VentCU/bbwtb/electronics/schematics/variantA.png

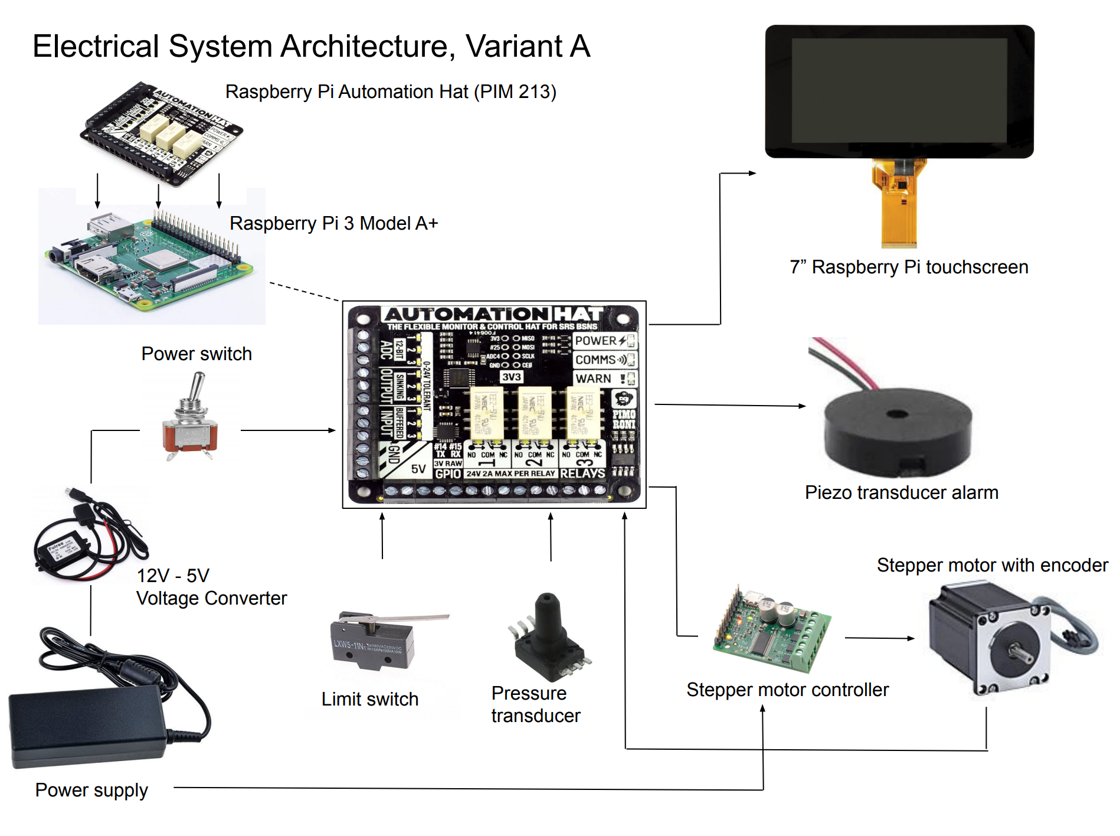
electronics/schematics/variantA.png
