VentCU/bbwtb/electronics/schematics/variantB.png

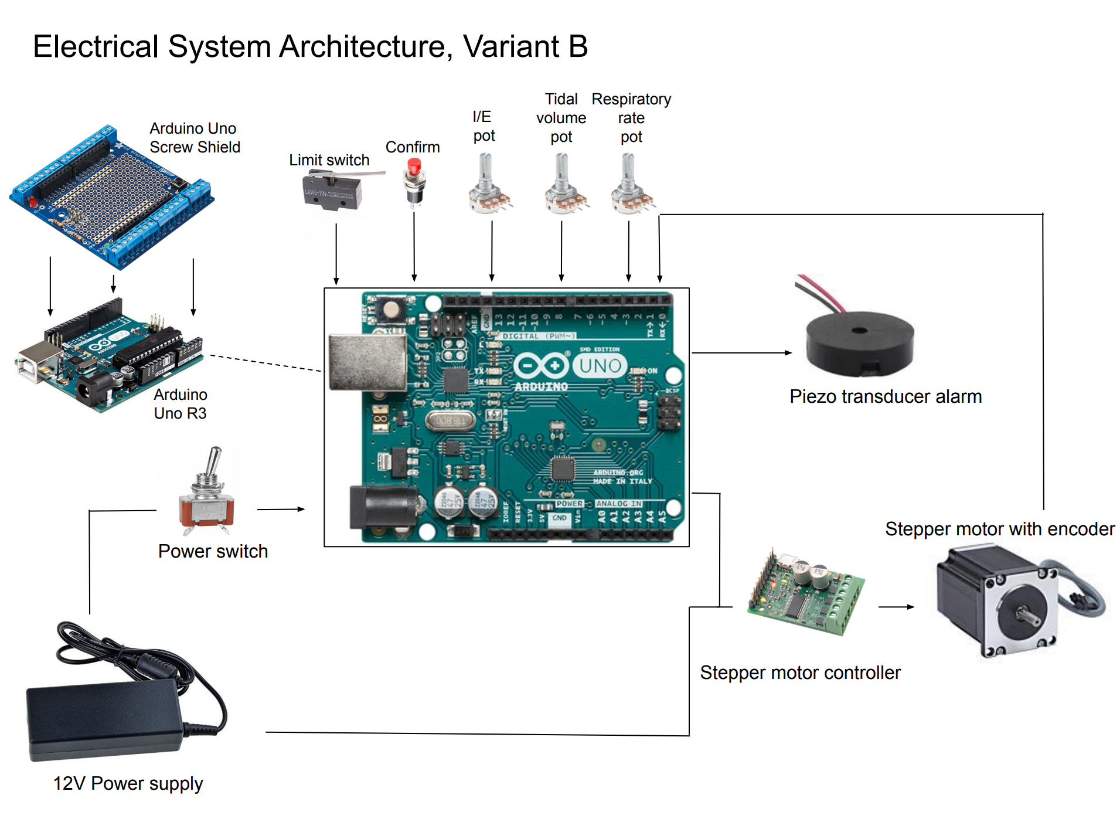
electronics/schematics/variantB.png
