VentCU/bbwtb/media/controls_labeled_exploded.jpg

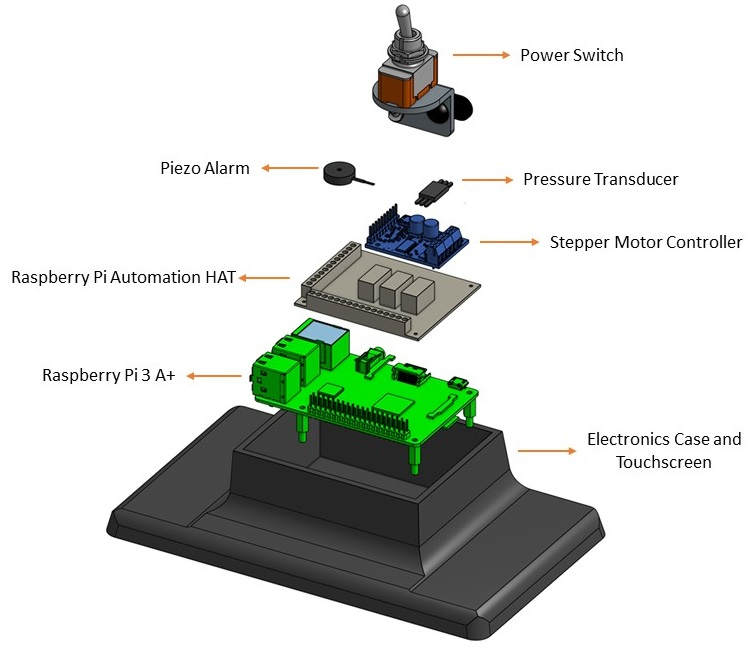
media/controls_labeled_exploded.jpg
