VentCU/bbwtb/media/frontleft_render.png

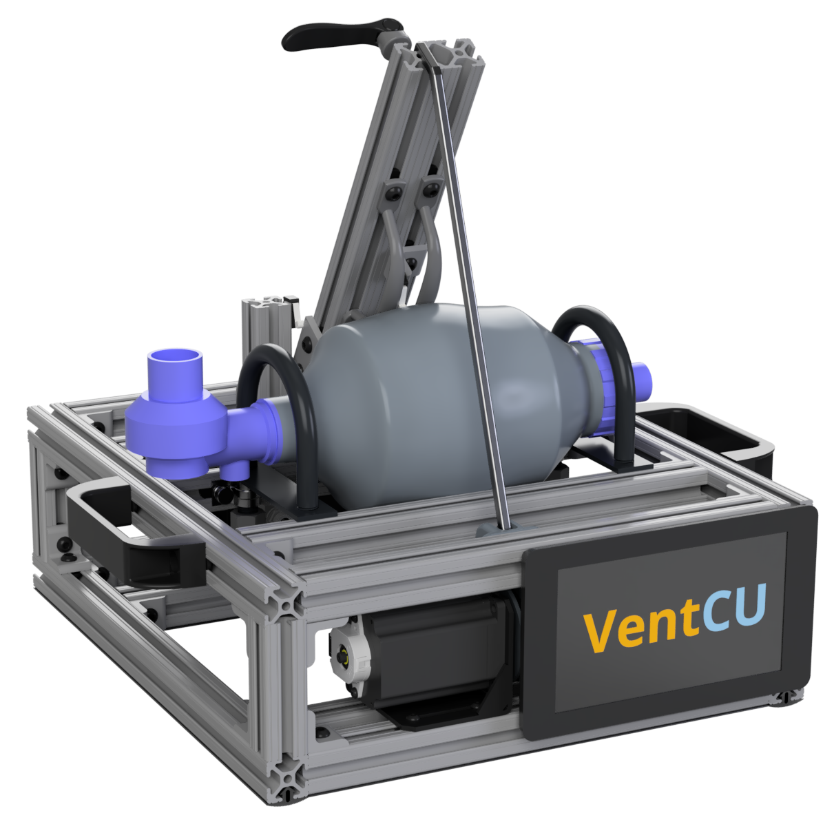
media/frontleft_render.png
