VentCU/bbwtb/media/labeled_exploded.jpg

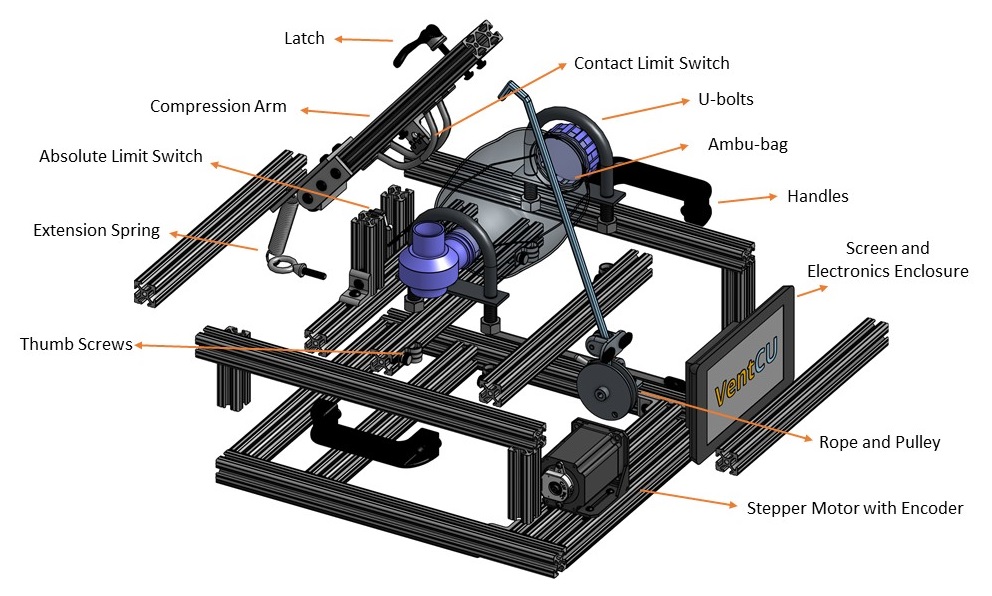
media/labeled_exploded.jpg
