VentCU/bbwtb/media/profiles/frontback.png

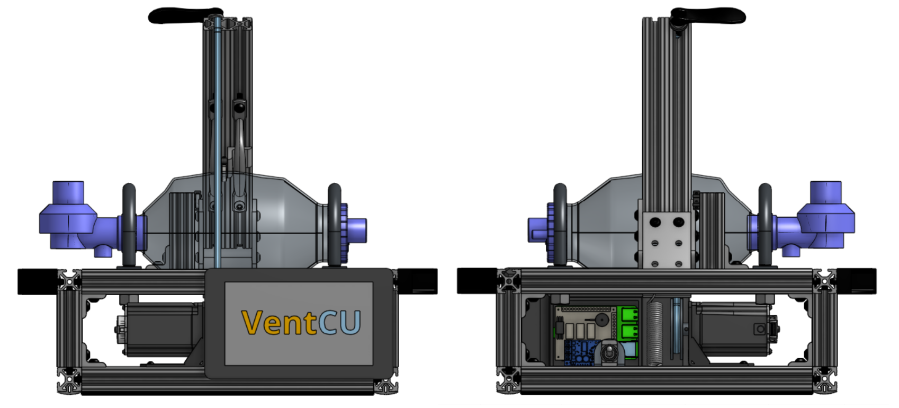
media/profiles/frontback.png
