VentCU/bbwtb/media/profiles/leftright.png

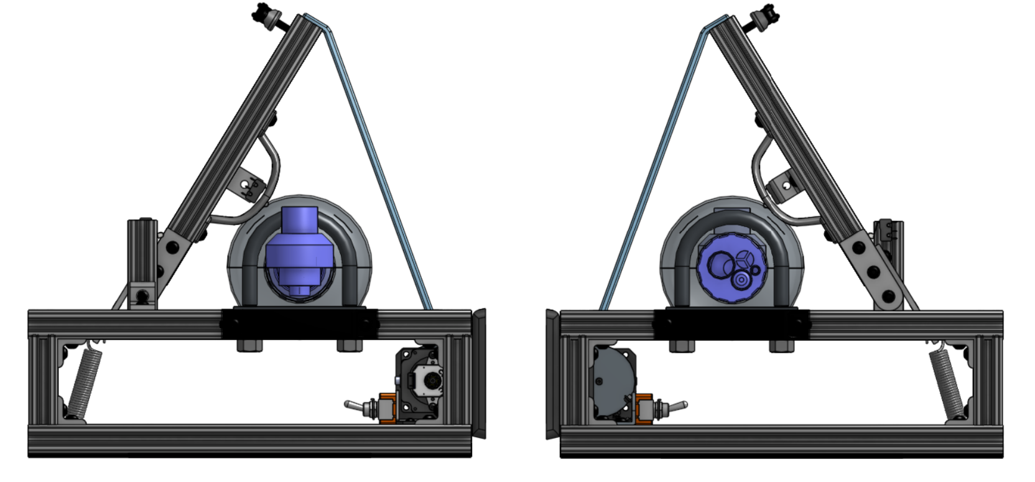
media/profiles/leftright.png
