VentCU/bbwtb/media/profiles/topbottom.png

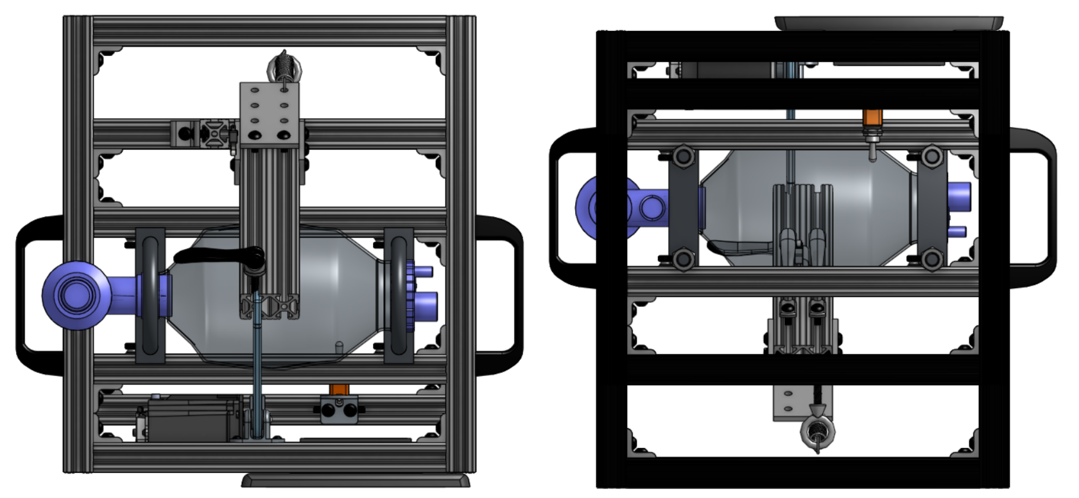
media/profiles/topbottom.png
