VentCU/bbwtb/media/render_with_ui.png

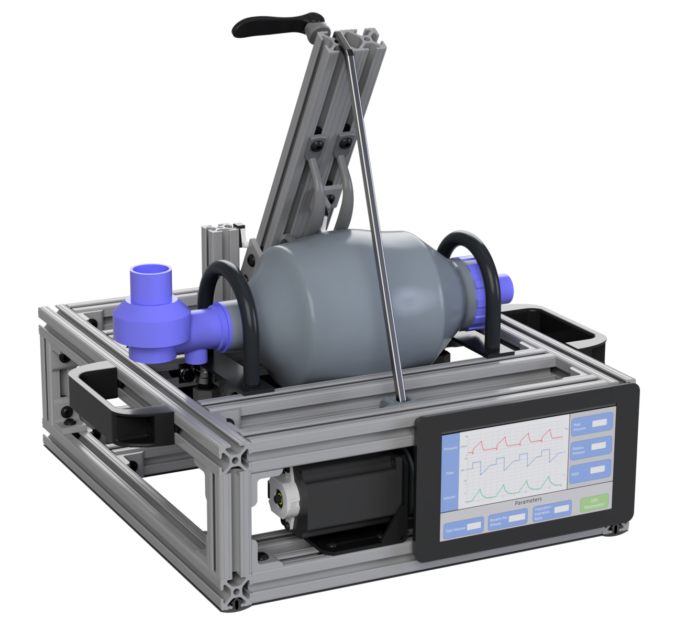
media/render_with_ui.png
