VentCU/bbwtb/media/v1/delphinefreebody.png

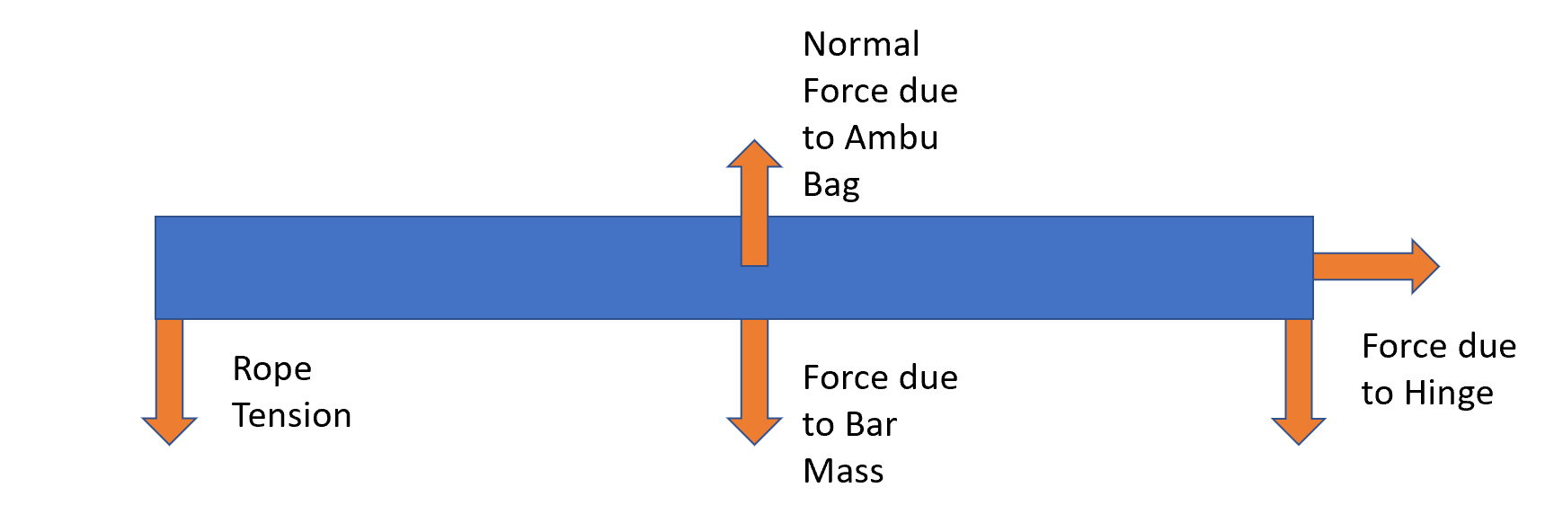
media/v1/delphinefreebody.png
