VentCU/bbwtb/media/v1/ventcu home view.PNG

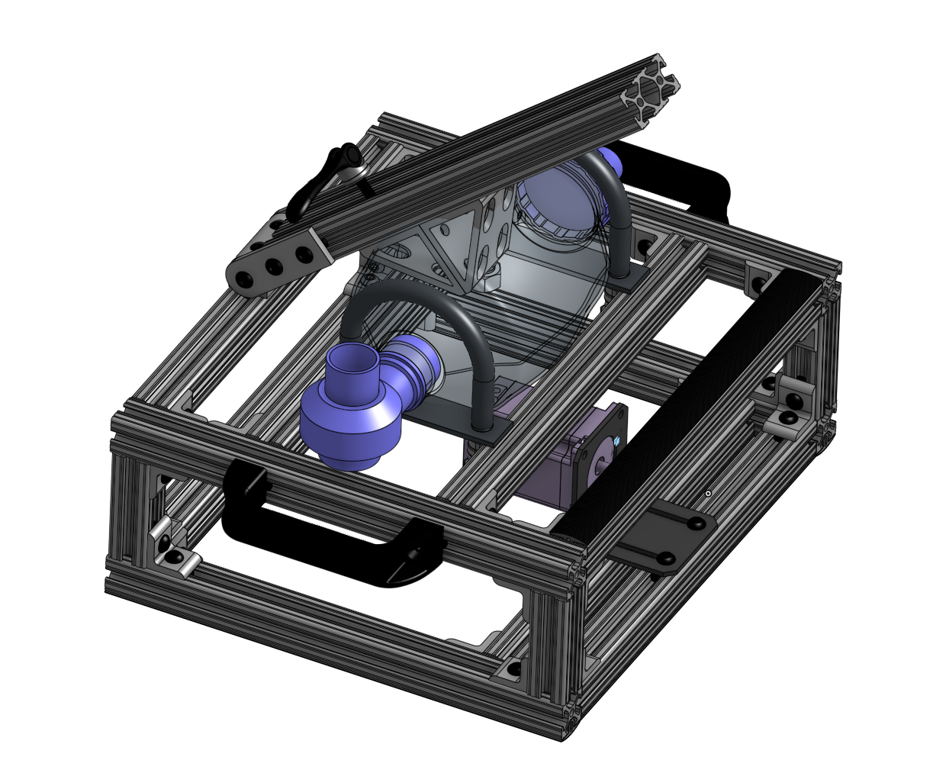
media/v1/ventcu home view.PNG
