VentCU/bbwtb/software/documentation/mock_ui.png

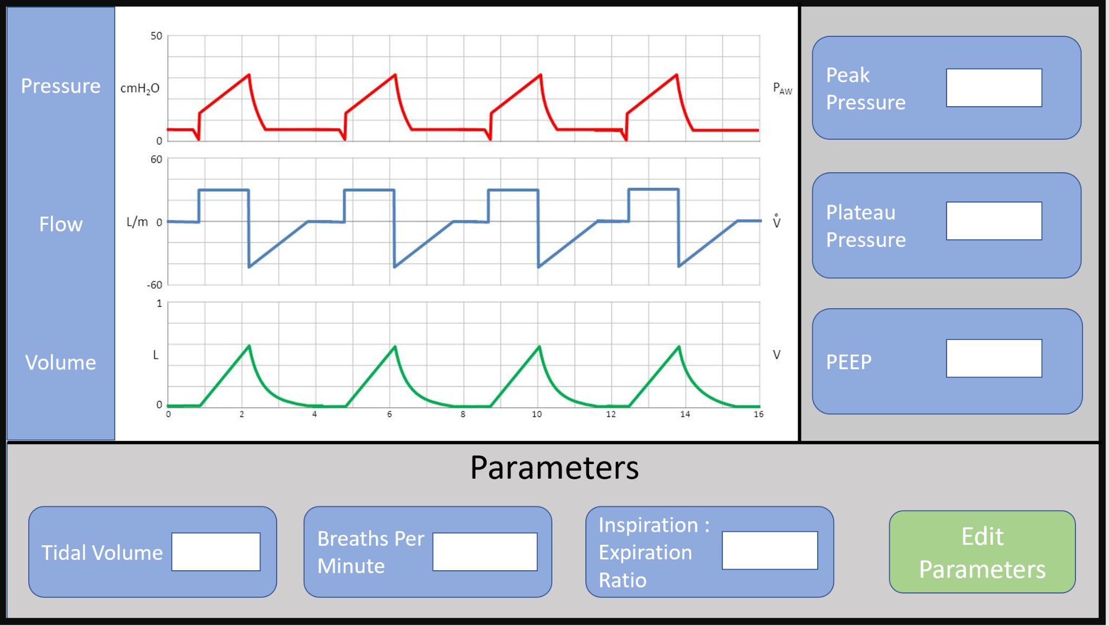
software/documentation/mock_ui.png
