VentCU/bbwtb/software/documentation/ui_alarm.PNG

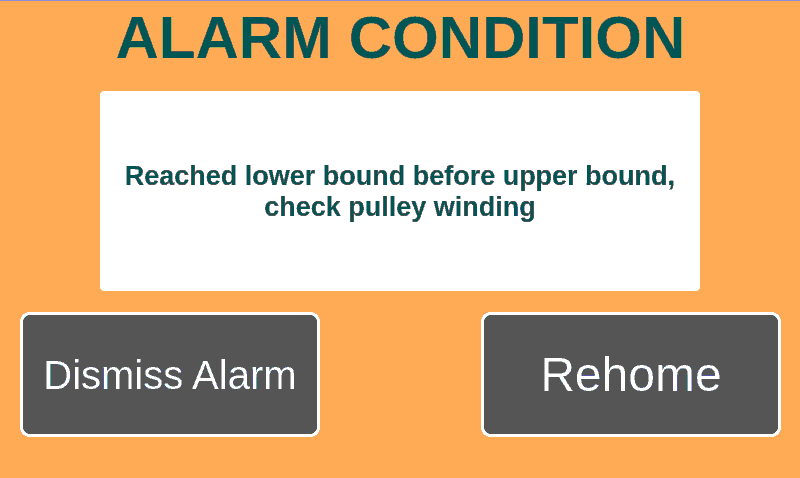
software/documentation/ui_alarm.PNG
