VentCU/bbwtb/software/documentation/ui_confirm_param.PNG

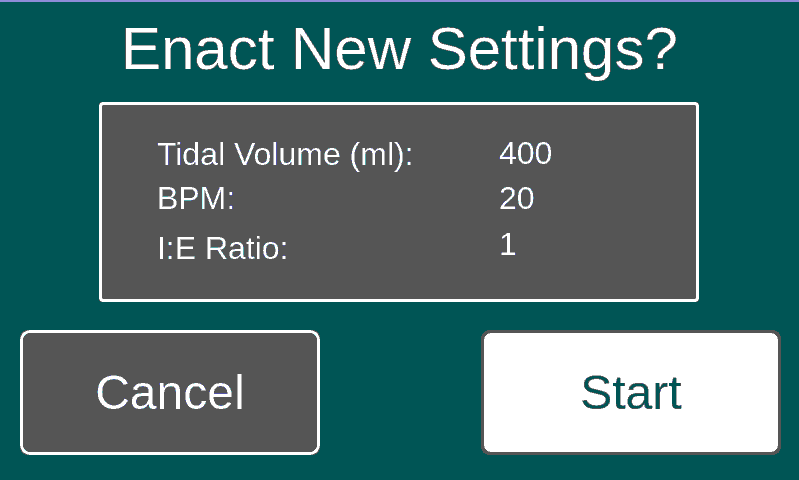
software/documentation/ui_confirm_param.PNG
