VentCU/bbwtb/software/documentation/ui_edit_param.PNG

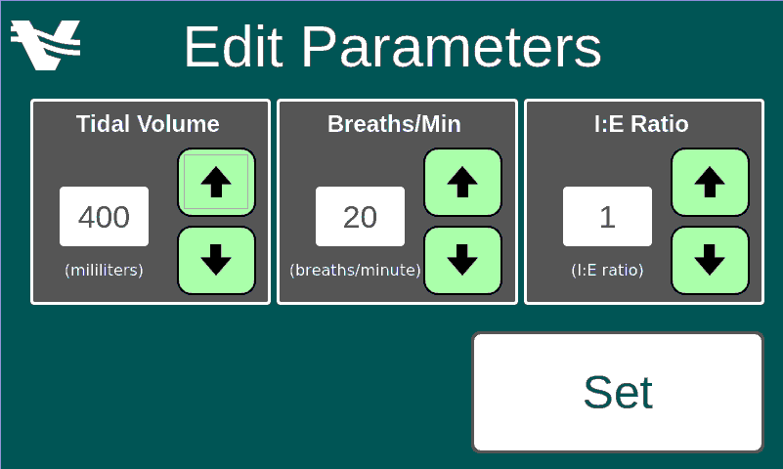
software/documentation/ui_edit_param.PNG
