VentCU/bbwtb/software/documentation/ui_home.PNG

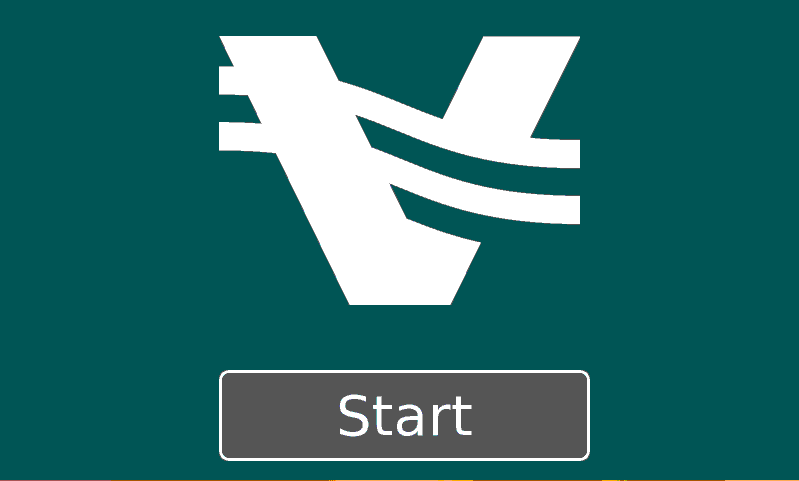
software/documentation/ui_home.PNG
