VentCU/bbwtb/software/documentation/ui_homing.PNG

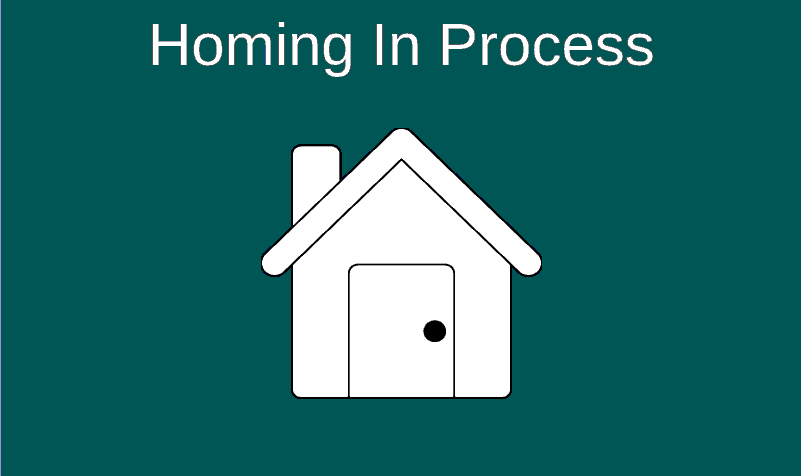
software/documentation/ui_homing.PNG
