VentCU/bbwtb/software/documentation/ui_main_page.PNG

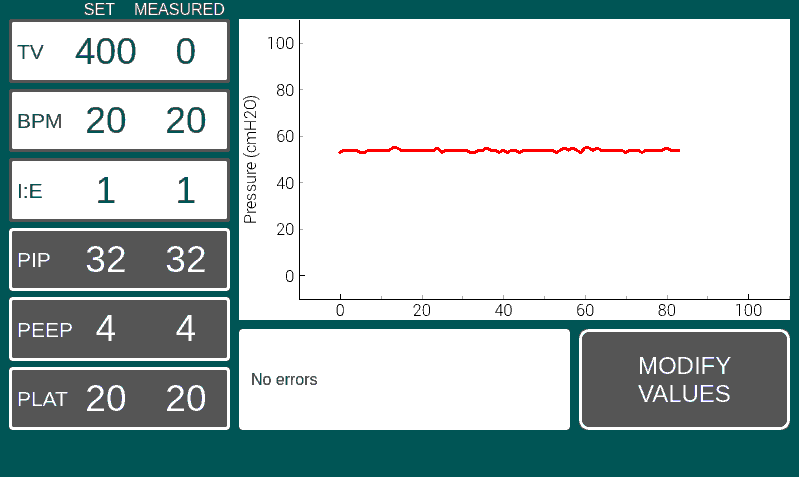
software/documentation/ui_main_page.PNG
