VentCU/bbwtb/media/v1/Case Assembly exploded view labeled.png

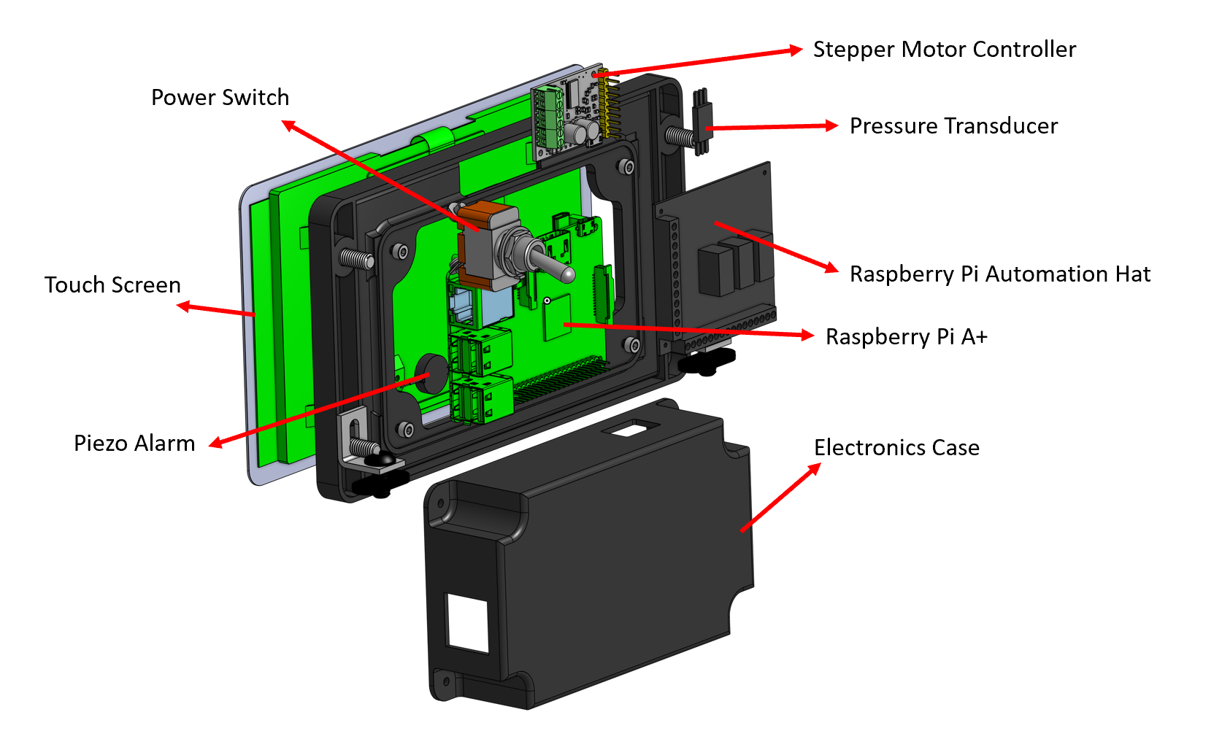
media/v1/Case Assembly exploded view labeled.png
