VentCU/bbwtb/media/v1/Case Assembly exploded view.png

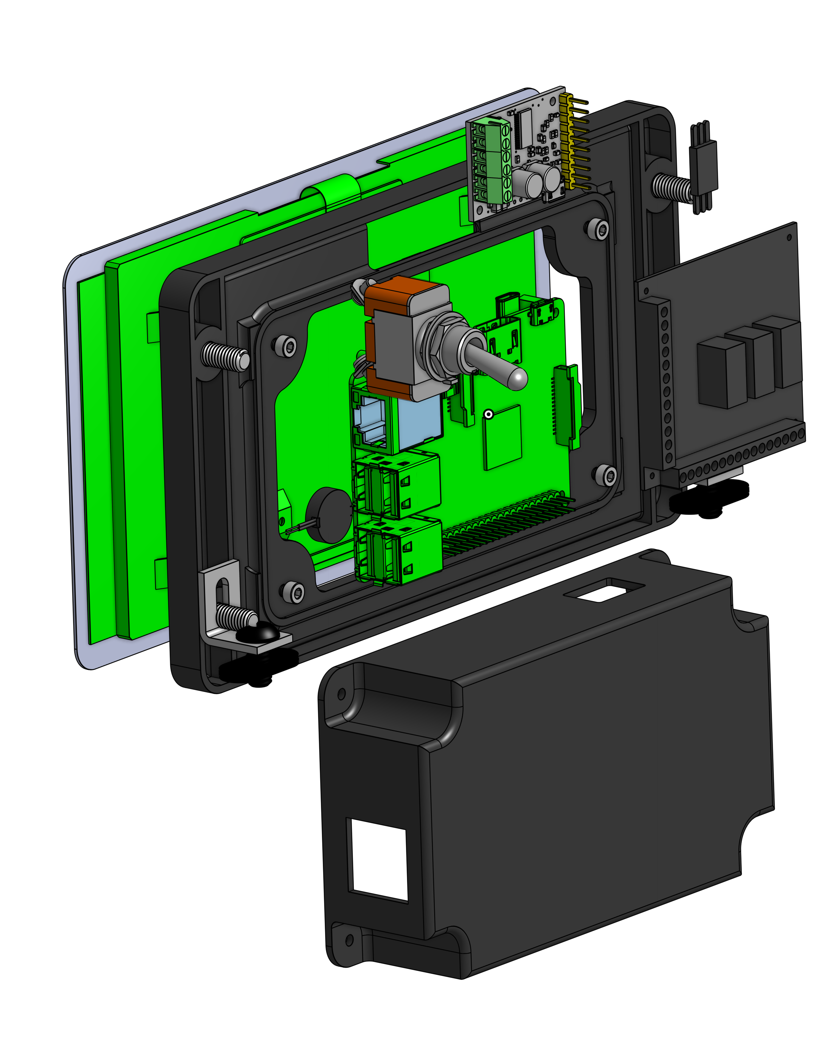
media/v1/Case Assembly exploded view.png
