VentCU/bbwtb/media/v1/Main Assembly back view.png

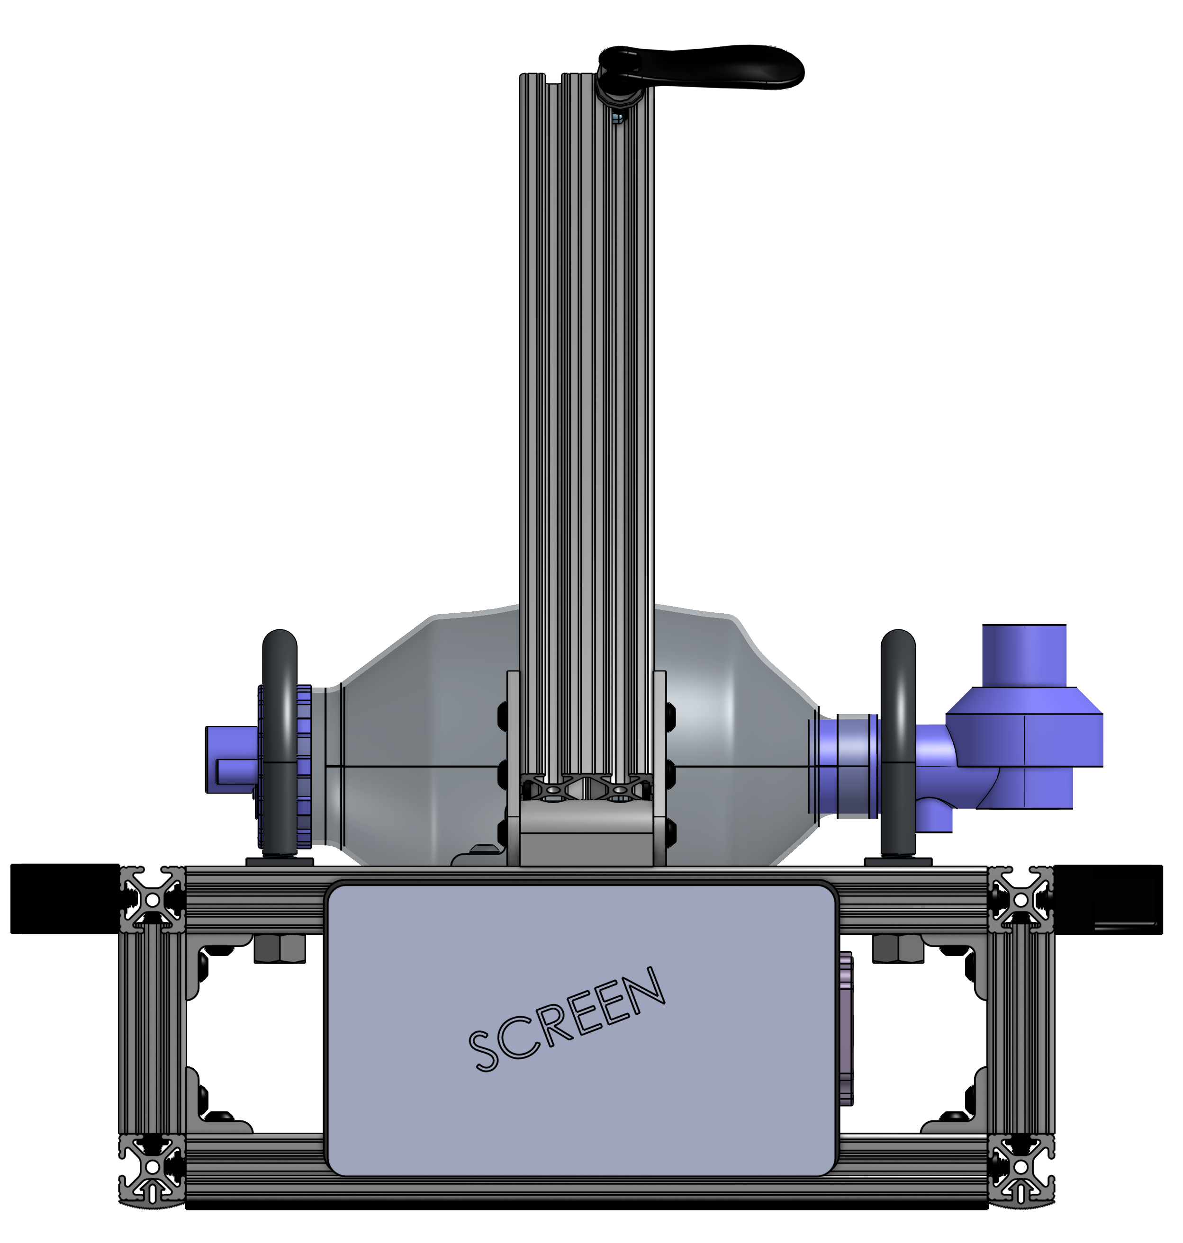
media/v1/Main Assembly back view.png
