VentCU/bbwtb/media/v1/Main Assembly bad render.png

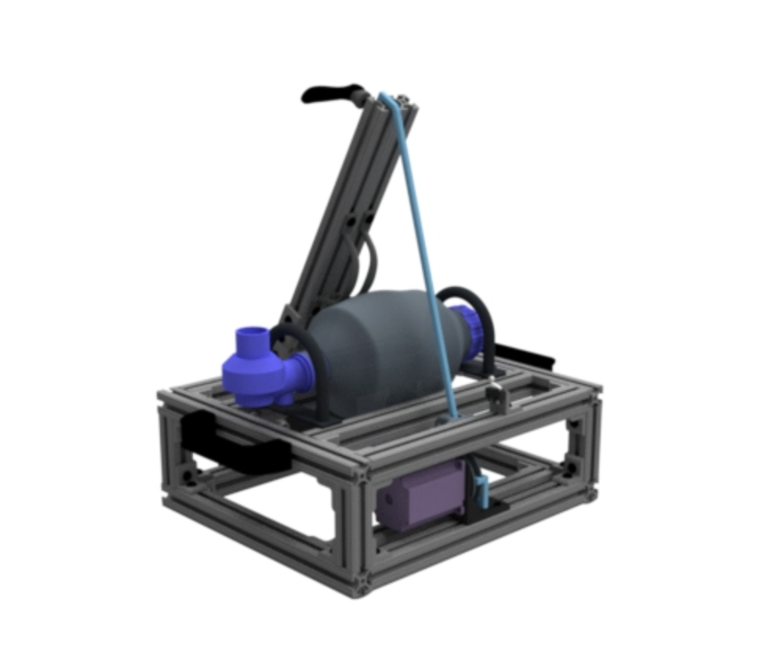
media/v1/Main Assembly bad render.png
