VentCU/bbwtb/media/v1/Main Assembly bottom view.png

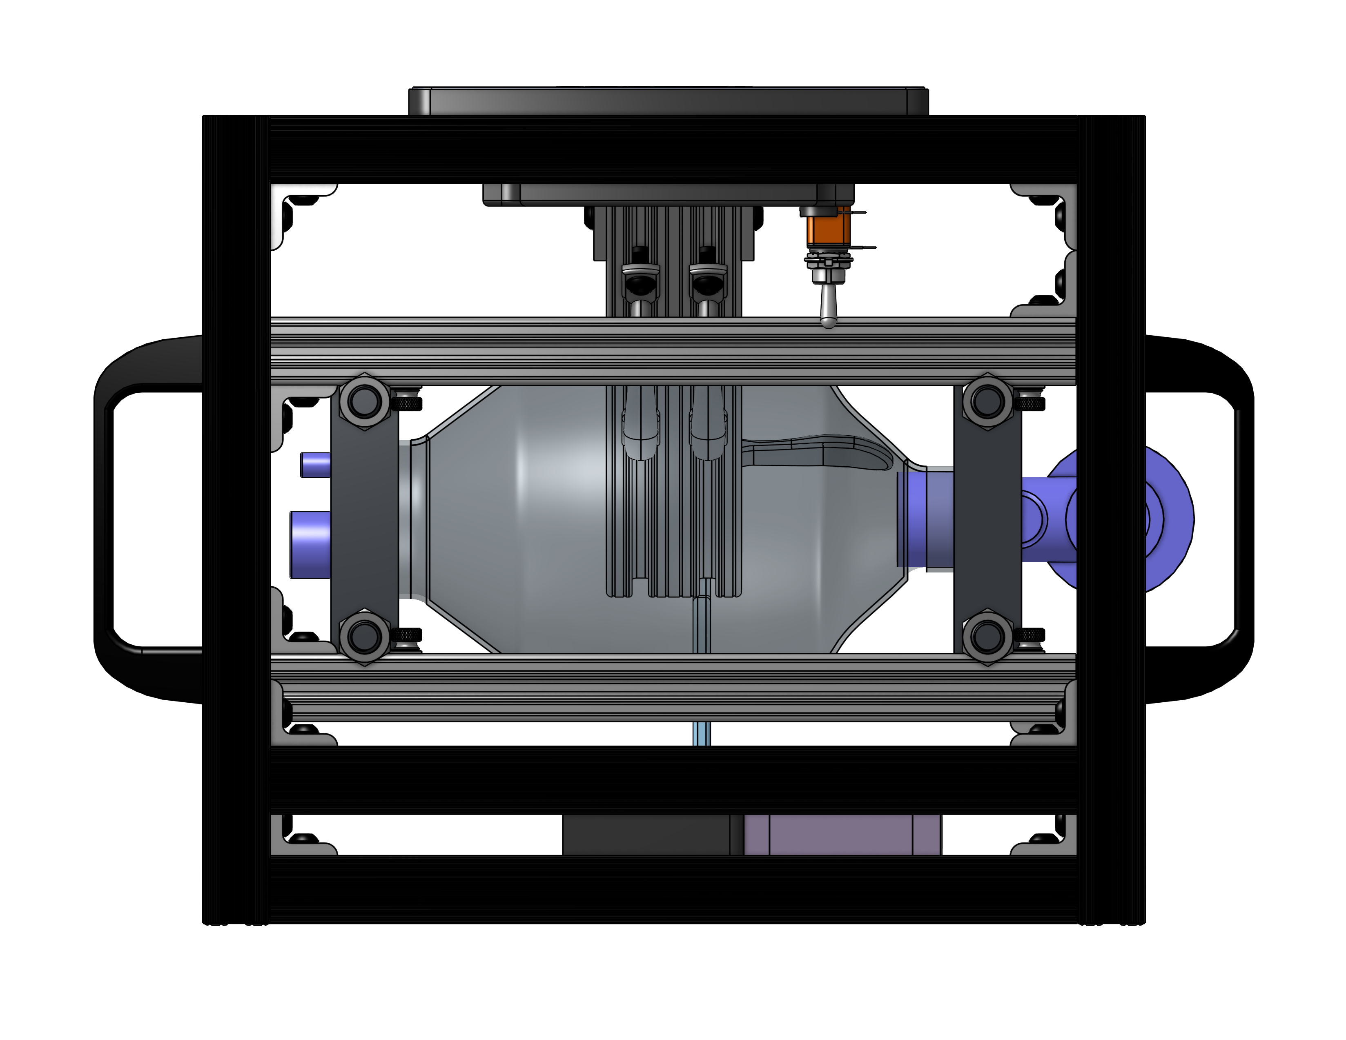
media/v1/Main Assembly bottom view.png
