VentCU/bbwtb/media/v1/Main Assembly exploded view labeled.png

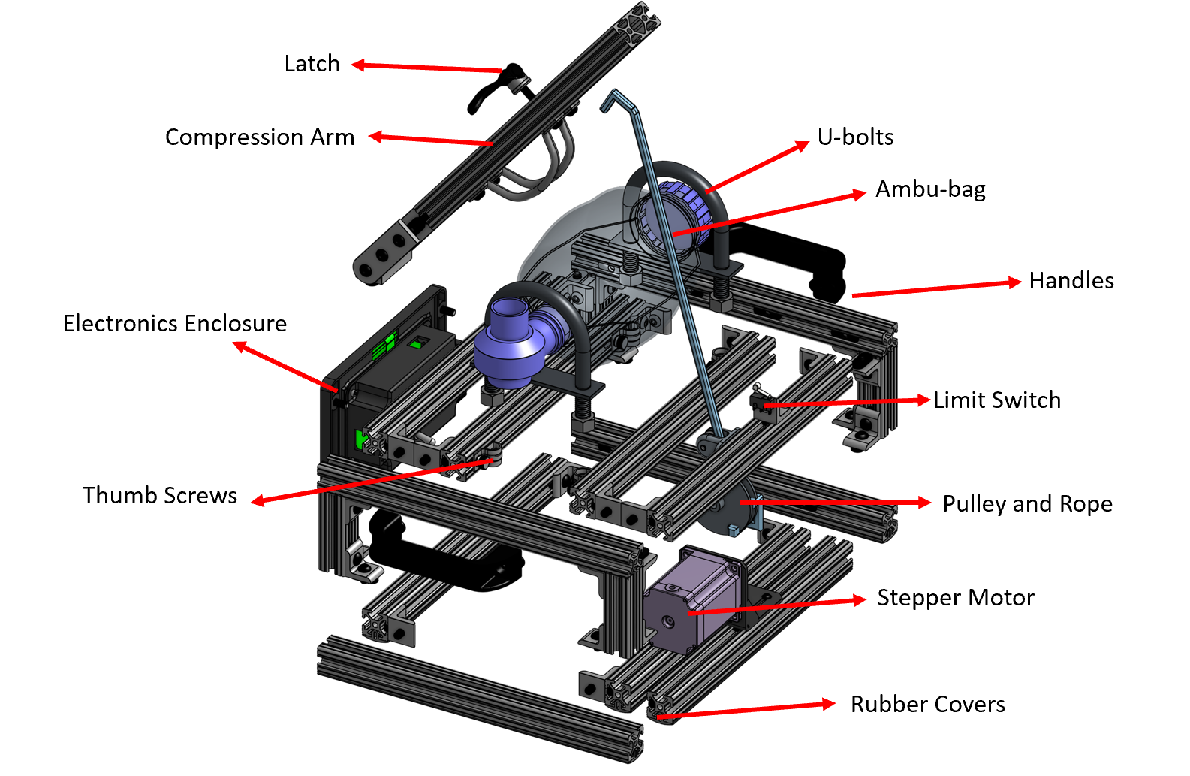
media/v1/Main Assembly exploded view labeled.png
