VentCU/bbwtb/media/v1/Main Assembly front and back view.png

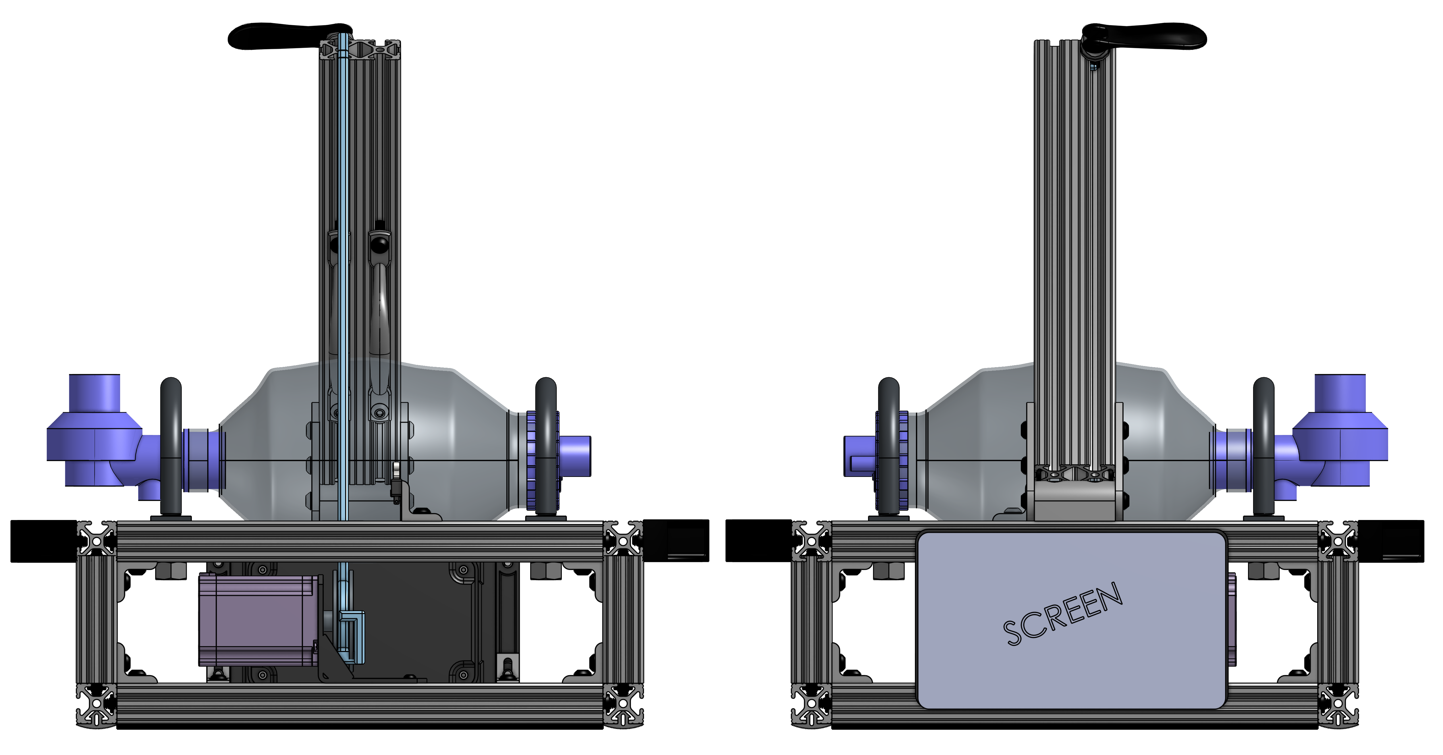
media/v1/Main Assembly front and back view.png
