VentCU/bbwtb/media/v1/Main Assembly home view alt.png

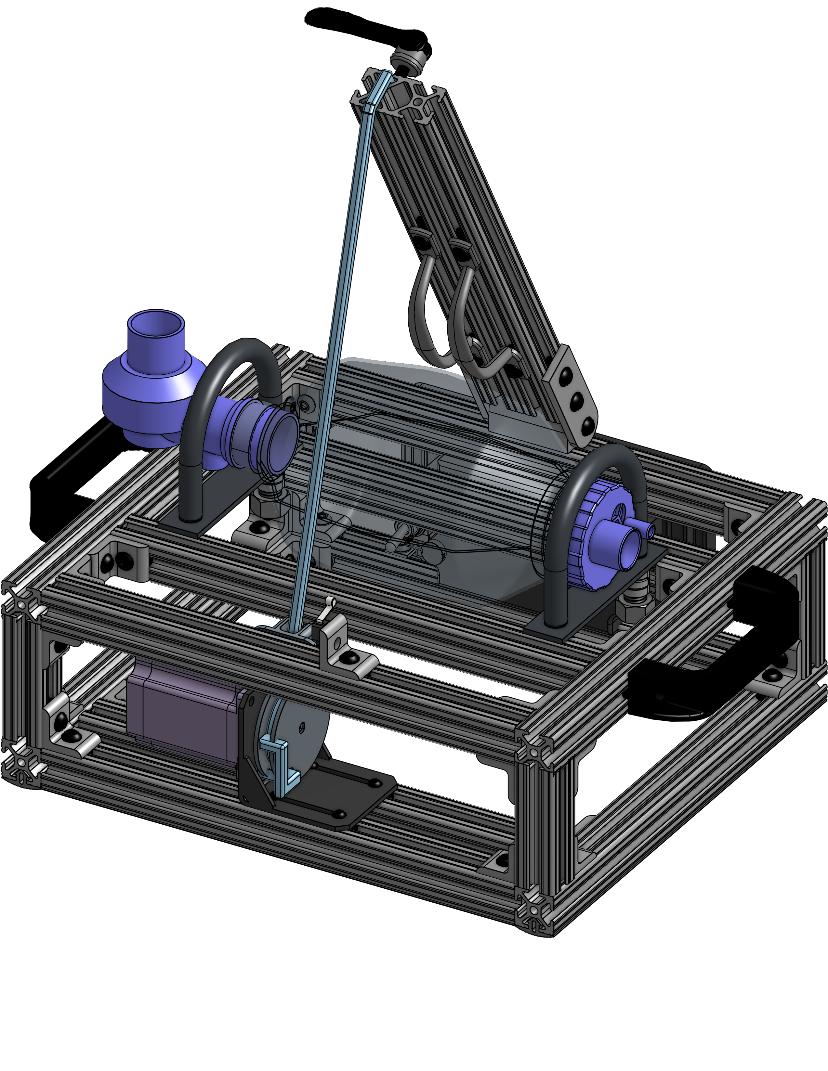
media/v1/Main Assembly home view alt.png
