VentCU/bbwtb/media/v1/Main Assembly left side view.png

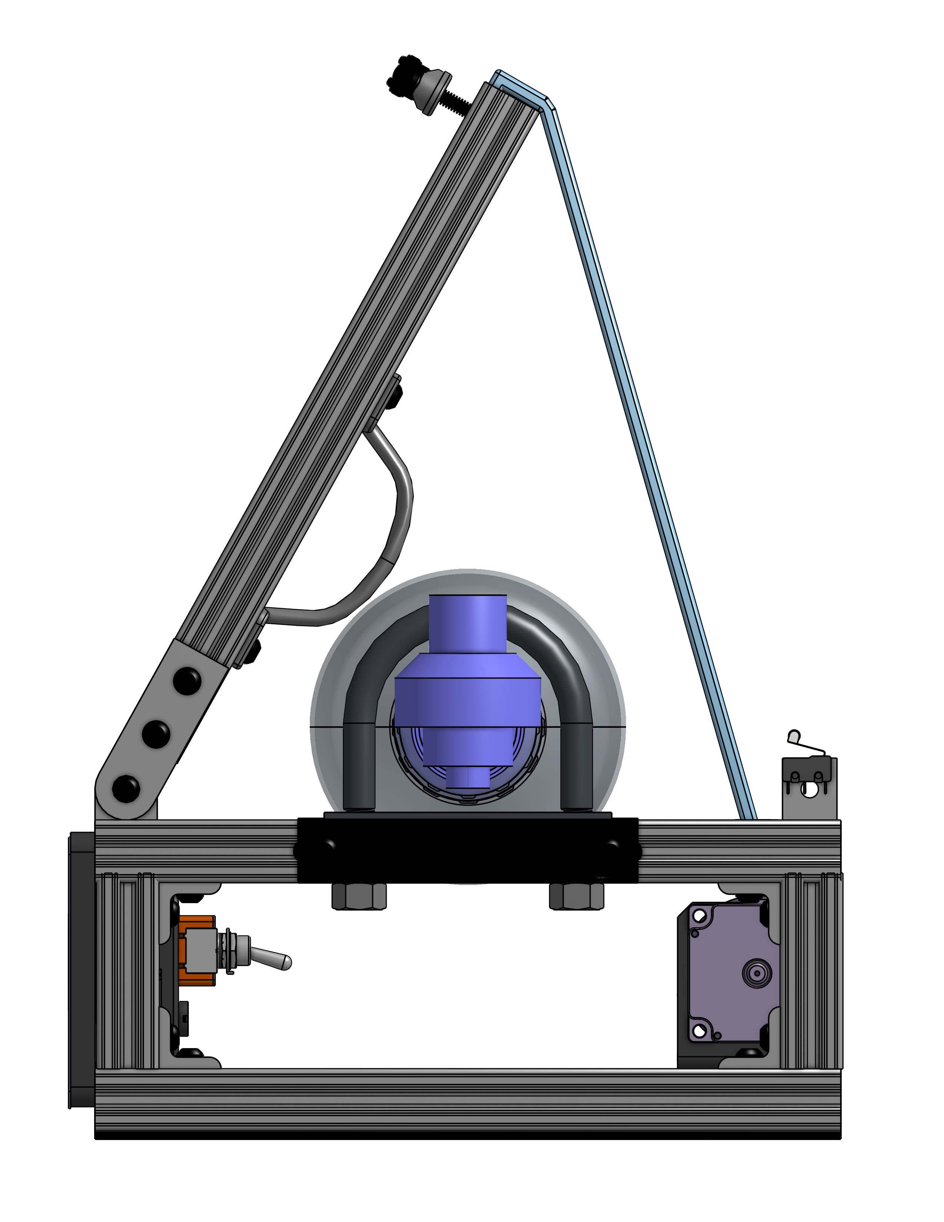
media/v1/Main Assembly left side view.png
