VentCU/bbwtb/media/v1/Main Assembly right side view.png

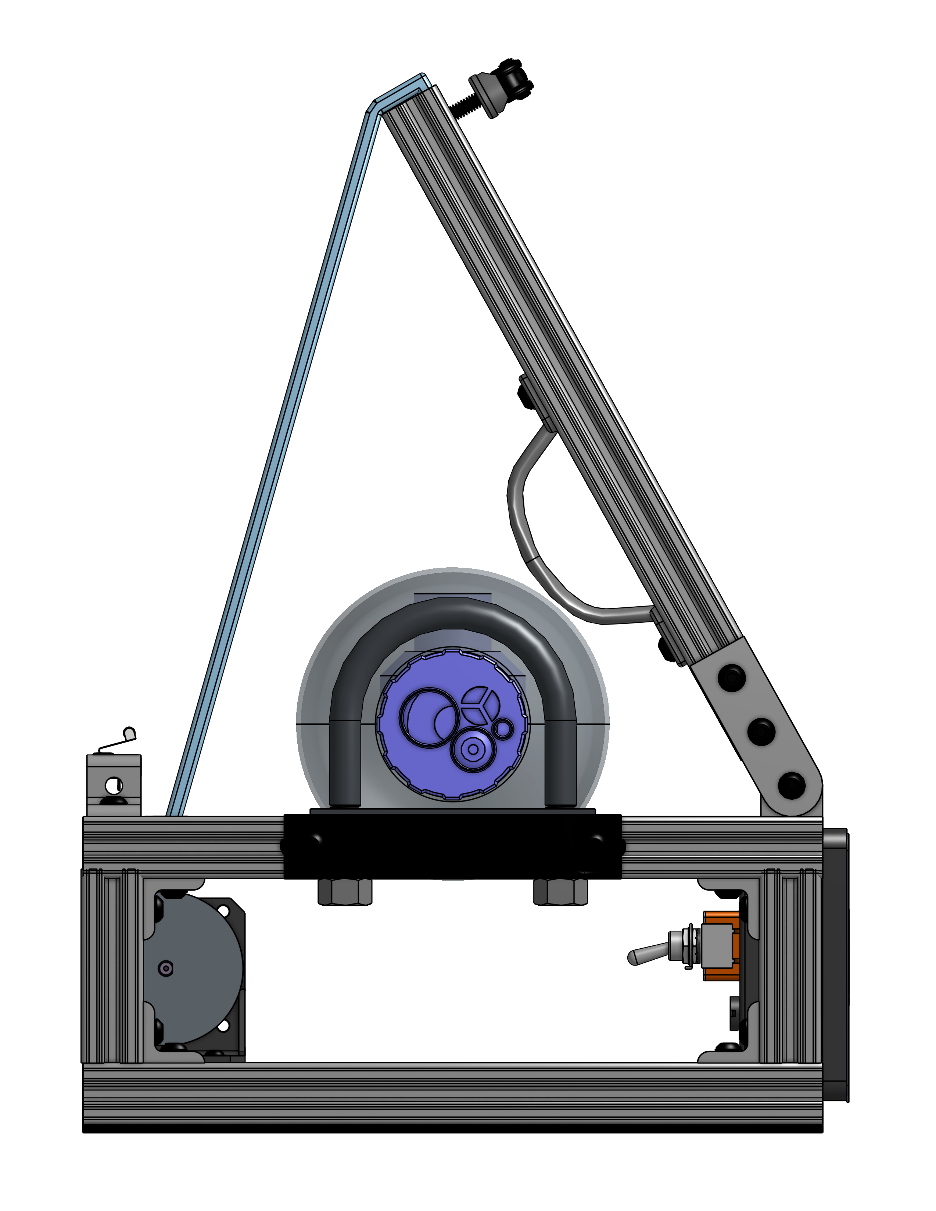
media/v1/Main Assembly right side view.png
