VentCU/bbwtb/media/v1/Main Assembly top and bottom view.png

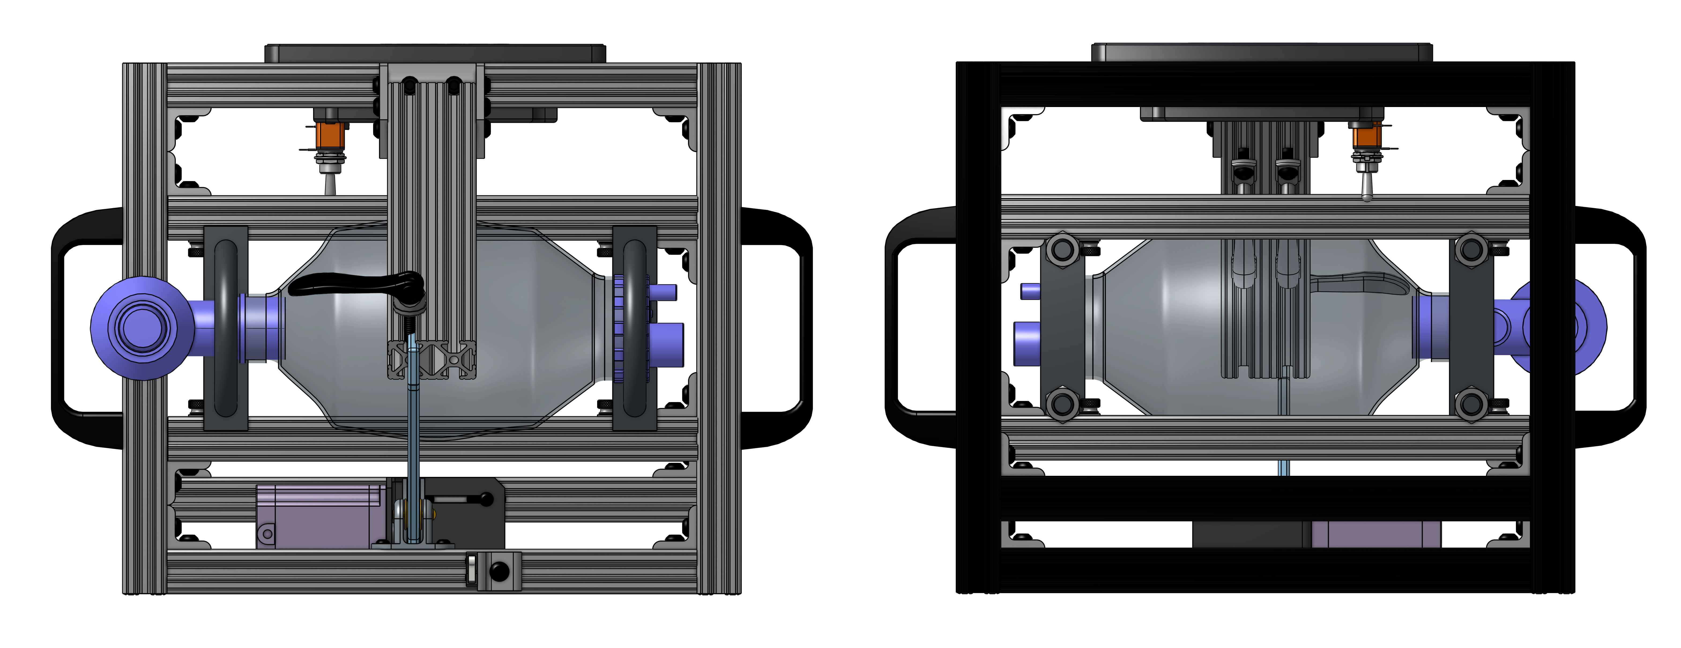
media/v1/Main Assembly top and bottom view.png
