VentCU/bbwtb/software/documentation/ui_homing_verif.PNG

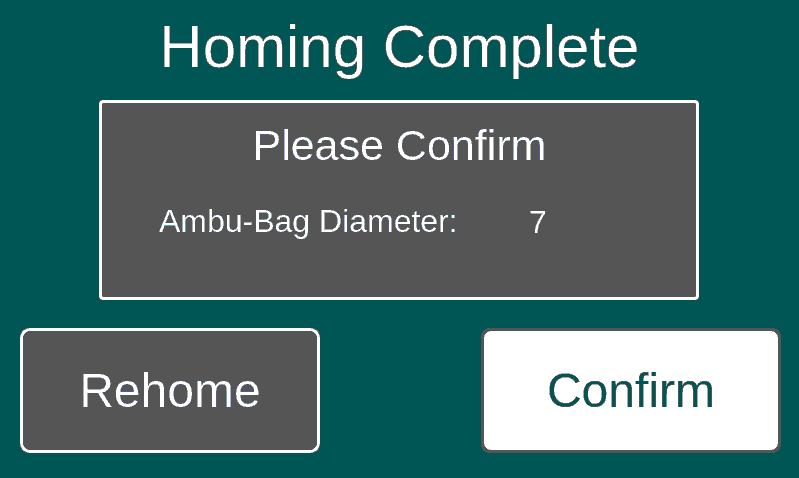
software/documentation/ui_homing_verif.PNG
