VentCU/bbwtb/software/control_system/sensors/rotary_encoder.py

import pigpio


class RotaryEncoder:
    """Class to decode mechanical rotary encoder pulses."""

    def __init__(self, pi, gpioA, gpioB):

        self.pi = pi
        self.gpioA = gpioA
        self.gpioB = gpioB

        self.encoder_value = 0
        self.levA = 0
        self.levB = 0

        self.lastGpio = None

        self.pi.set_mode(gpioA, pigpio.INPUT)
        self.pi.set_mode(gpioB, pigpio.INPUT)

        self.pi.set_pull_up_down(gpioA, pigpio.PUD_UP)
        self.pi.set_pull_up_down(gpioB, pigpio.PUD_UP)

        self.cbA = self.pi.callback(gpioA, pigpio.EITHER_EDGE, self._pulse)
        self.cbB = self.pi.callback(gpioB, pigpio.EITHER_EDGE, self._pulse)

    def _pulse(self, gpio, level, tick):

        """
      Decode the rotary encoder pulse.

                   +---------+         +---------+      0
                   |         |         |         |
         A         |         |         |         |
                   |         |         |         |
         +---------+         +---------+         +----- 1

             +---------+         +---------+            0
             |         |         |         |
         B   |         |         |         |
             |         |         |         |
         ----+         +---------+         +---------+  1
      """

        if gpio == self.gpioA:
            self.levA = level
        else:
            self.levB = level

        if gpio != self.lastGpio:  # debounce
            self.lastGpio = gpio

            if gpio == self.gpioA and level == 1:
                if self.levB == 1:
                    self.callback(1)
            elif gpio == self.gpioB and level == 1:
                if self.levA == 1:
                    self.callback(-1)

    def cancel(self):
        self.cbA.cancel()
        self.cbB.cancel()

    def callback(self, value):
        self.encoder_value += value

    def value(self):
        return self.encoder_value

    def reset_position(self):
        self.encoder_value = 0
