VentCU/bbwtb/software/control_system/ui_controller_interface.py

#
# UIControllerInterface class
# VentCU - An open source ventilator
#
# (c) VentCU, 2020. All Rights Reserved.
#

import logging
from time import sleep
import threading

from alarms.alarm_handler import AlarmHandler
from alarms.alarms import *

from PyQt5 import QtCore
from PyQt5.QtGui import *
from PyQt5.QtCore import *
from PyQt5.QtWidgets import *

# Worker takes in a function and runs it within a QRunnable
# so that in can run in a separate thread within the QThreadPool
# https://www.learnpyqt.com/courses/concurrent-execution/multithreading-pyqt-applications-qthreadpool/
class Worker(QRunnable):
    """
    Worker thread

    Inherits from QRunnable to handler worker thread setup, signals and wrap-up.

    :param callback: The function callback to run on this worker thread. Supplied args and
                     kwargs will be passed through to the runner.
    :type callback: function
    :param args: Arguments to pass to the callback function
    :param kwargs: Keywords to pass to the callback function

    """
    def __init__(self, fn, *args, **kwargs):
        super(Worker, self).__init__()
        self.fn = fn
        self.args = args
        self.kwargs = kwargs

    @pyqtSlot()
    def run(self):
        """
        Initialise the runner function with passed args, kwargs
        """
        self.fn(*self.args, **self.kwargs)


class UIControllerInterface:

    def __init__(self, ventilator_ui, ventilator_controller):
        self.logger = logging.getLogger('ui_controller_interface')
        
        self.ui = ventilator_ui
        self.controller = ventilator_controller

        self.threadpool = QThreadPool()
        self.alarm_handler = AlarmHandler(self.ui, self.controller)
        threading.excepthook = self.except_alarm_hook

        self.modified_volume = self.controller.volume
        self.modified_bpm = self.controller.bpm
        self.modified_ie = self.controller.ie
        self.last_controller_state = None
        self.interface_elements()

        self.ventilate_thread_spawned = False

    def interface_elements(self):

        self.controller.state_change_sender.state_change_signal.connect(
            lambda: self.state_change()
        )

        self.controller.shutdown_sender.shutdown_signal.connect(
            lambda: self.try_controller_method( self.controller.set_state, parameters=self.controller.OFF_STATE )
        )
        
        """
        alarm window elements
        """
        self.controller.alarm_sender.alarm_signal.connect(
            self.except_alarm_hook
        )
        self.ui.stack.alarm_condition.rehome_button.clicked.connect(
            lambda: self.try_controller_method( self.controller.set_state, parameters=self.controller.HOMING_STATE )
        )
        self.ui.stack.alarm_condition.dismiss_alarm_button.clicked.connect(
            self.dismiss_alarm_handler 
        )
        
        """
        start_homing window elements
        """
        self.ui.stack.start_homing.start_button.clicked.connect(
            lambda: self.try_controller_method( self.controller.set_state, parameters=self.controller.HOMING_STATE )
        )

        """
        confirm_homing window elements
        """
        self.ui.stack.confirm_homing.rehome_button.clicked.connect(
            lambda: self.try_controller_method( self.controller.set_state, parameters=self.controller.HOMING_STATE )
        )

        self.update_label(self.ui.stack.confirm_homing.bag_size_label, self.controller.bag_size)     # TODO: format text as inches

        """
        edit_parameters window elements
        """
        def update_edit_parameters_elements():
            if self.controller.current_state is self.controller.HOMING_VERIF_STATE:
                self.ui.stack.edit_parameters.back_button.hide()
            else:
                self.ui.stack.edit_parameters.back_button.show()

        self.ui.stack.confirm_homing.confirm_button.clicked.connect(update_edit_parameters_elements)
        self.ui.stack.main_window.edit_parameters_button.clicked.connect(update_edit_parameters_elements)

        self.update_label(self.ui.stack.edit_parameters.TV_label, self.controller.volume)
        self.update_label(self.ui.stack.edit_parameters.BPM_label, self.controller.bpm)
        self.update_label(self.ui.stack.edit_parameters.IE_label, self.controller.ie)
        self.controller.measured_parameters_sender.update_measured_parameters_signal.connect(
            self.update_measured_parameters 
        )
        
        # TODO: redefine logical values for increasing and decreasing
        self.ui.stack.edit_parameters.tidal_increase_button.clicked.connect(
            lambda: self.modify_interface_parameters(volume=self.modified_volume + 10)
        )
        self.ui.stack.edit_parameters.tidal_decrease_button.clicked.connect(
            lambda: self.modify_interface_parameters(volume=self.modified_volume - 10)
        )
        self.ui.stack.edit_parameters.bpm_increase_button.clicked.connect(
            lambda: self.modify_interface_parameters(bpm=self.modified_bpm + 1)
        )
        self.ui.stack.edit_parameters.bpm_decrease_button.clicked.connect(
            lambda: self.modify_interface_parameters(bpm=self.modified_bpm - 1)
        )
        self.ui.stack.edit_parameters.ie_increase_button.clicked.connect(
            lambda: self.modify_interface_parameters(ie=self.modified_ie + 1)
        )
        self.ui.stack.edit_parameters.ie_decrease_button.clicked.connect(
            lambda: self.modify_interface_parameters(ie=self.modified_ie - 1)
        )

        """
        confirm_parameters window elements
        """
        def update_confirm_parameters_elements():
            if self.controller.current_state is self.controller.HOMING_VERIF_STATE:
                self.update_label(self.ui.stack.confirm_parameters.confirm_button, "Start")
            else:
                self.update_label(self.ui.stack.confirm_parameters.confirm_button,  "Confirm" )

            self.update_label(self.ui.stack.confirm_parameters.confirm_TV_label, self.modified_volume)
            self.update_label(self.ui.stack.confirm_parameters.confirm_BPM_label, self.modified_bpm)
            self.update_label(self.ui.stack.confirm_parameters.confirm_IE_label, self.modified_ie)

        self.ui.stack.edit_parameters.set_button.clicked.connect(update_confirm_parameters_elements)

        # begin main ventilate thread
        self.ui.stack.confirm_parameters.confirm_button.clicked.connect(
            lambda: self.update_parameters()
        )

        """
        main_window window elements
        """
        self.update_label(self.ui.stack.main_window.set_TV_label, self.controller.volume)
        self.update_label(self.ui.stack.main_window.set_BPM_label, self.controller.bpm)
        self.update_label(self.ui.stack.main_window.set_IE_label, self.controller.ie)

        # TODO: connect graph to pressure data from controller

        # connect gui close to motor destructor
        self.ui.app.aboutToQuit.connect(self.controller.stop_ventilation)

    def modify_interface_parameters(self, volume=None, bpm=None, ie=None):
        # update local modified parameters
        if volume: self.modified_volume = volume    # TODO: add bounds
        if bpm: self.modified_bpm = bpm             # TODO: add bounds
        if ie: self.modified_ie = ie                # TODO: add bounds

        # update display elements
        self.update_label(self.ui.stack.edit_parameters.TV_label, self.modified_volume)
        self.update_label(self.ui.stack.edit_parameters.BPM_label, self.modified_bpm)
        self.update_label(self.ui.stack.edit_parameters.IE_label, self.modified_ie)

    # spawns ventilate thread if updating for the first time
    def update_parameters(self):
        # update controller parameters from interface parameters
        self.try_controller_method( self.controller.update_tidal_volume, parameters=self.modified_volume )
        self.try_controller_method( self.controller.update_bpm, parameters=self.modified_bpm )
        self.try_controller_method( self.controller.update_ie, parameters=self.modified_ie )

        self.update_label(self.ui.stack.main_window.set_TV_label, self.modified_volume)
        self.update_label(self.ui.stack.main_window.set_BPM_label, self.modified_bpm)
        self.update_label(self.ui.stack.main_window.set_IE_label, self.modified_ie)
        
        if( not self.ventilate_thread_spawned ):
            # spawn ventilate thread
            self.new_thread("ventilate_thread", self.controller.start_ventilation)
            self.ventilate_thread_spawned = True
            
    # updates measured parameters at a constant frequency, unlike "update_parameters(self)" which is on button signal
    def update_measured_parameters(self):
        self.update_label(self.ui.stack.main_window.measure_TV_label, int(self.controller.measure_volume))
        self.update_label(self.ui.stack.main_window.measure_BPM_label, round(self.controller.measure_bpm))
        self.update_label(self.ui.stack.main_window.measure_IE_label, self.controller.measure_ie["ie_ratio"])
     
    # dismissed alarms require different widget redirection depending on state 
    def dismiss_alarm_handler(self):
        if(self.last_controller_state is self.controller.HOMING_STATE
        or self.last_controller_state is self.controller.HOMING_VERIF_STATE ):
          self.ui.stack.QtStack.setCurrentWidget(self.ui.stack.start_homing)
        else:
          self.ui.stack.QtStack.setCurrentWidget(self.ui.stack.main_window)
          
    def update_label(self, label, value):
        label.setText( str(value) )

    def new_thread(self, name, target_method):
        worker = Worker(target_method)
        self.threadpool.start(worker)
        # print("New thread spawned: " + name)
        self.logger.info(f"New thread spawned: {name}")


    def start_homing(self):
        self.ui.stack.QtStack.setCurrentWidget(self.ui.stack.homing)
        self.new_thread("homing_thread", self.controller.start_homing)

    def state_change(self):
        # start homing if state changes to homing state
        if self.controller.current_state is self.controller.HOMING_STATE:
            self.start_homing()

        # switch window if homing successfuly completes
        if self.controller.current_state is self.controller.HOMING_VERIF_STATE:
            self.ui.stack.QtStack.setCurrentWidget(self.ui.stack.confirm_homing)

    def try_controller_method(self, method, state_to_set=None, parameters=None):
        if state_to_set is not None:
            self.controller.set_state(state_to_set)

        try:
            if parameters is None:
                method()
            else:
                method(parameters)
        except Alarm as alarm:
            self.alarm_handler.handle_alarms(alarm)

    def except_alarm_hook(self, alarm=None):
        self.last_controller_state = self.controller.current_state
        self.controller.set_state(self.controller.PAUSE_STATE)
        # set text
        self.ui.stack.alarm_condition.error_message_label.setText(alarm.message)
        # switch window if alarm raised
        self.ui.stack.QtStack.setCurrentWidget(self.ui.stack.alarm_condition)
        if isinstance( alarm, HOMING_ALARM):
            # TODO: verify that raising exception kills thread (UNLESS thread NEEDED)
            self.alarm_handler.handle_alarms(alarm) 
        elif isinstance( alarm, OVER_PRESSURE_ALARM):
            # TODO: verify that raising exception kills thread (UNLESS thread NEEDED)
            self.alarm_handler.handle_alarms(alarm)  
        elif isinstance( alarm, UNDER_PRESSURE_ALARM):
            # TODO: verify that raising exception kills thread (UNLESS thread NEEDED)
            self.alarm_handler.handle_alarms(alarm)  
        elif isinstance( alarm, POSITION_ALARM):
            # TODO: verify that raising exception kills thread (UNLESS thread NEEDED)
            self.alarm_handler.handle_alarms(alarm) 
        elif isinstance( alarm, SYSTEM_ALARM):
            # TODO: verify that raising exception kills thread (UNLESS thread NEEDED)
            self.alarm_handler.handle_alarms(alarm) 
        else:
            raise alarm
